FromentLorenzo/2024InternshipWatermeterAICam/test pictures/5.jpg

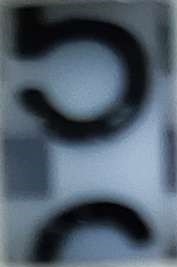
test pictures/5.jpg
