FromentLorenzo/2024InternshipWatermeterAICam/test pictures/8.jpg

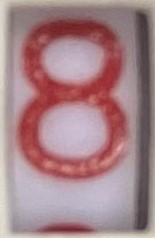
test pictures/8.jpg
