FromentLorenzo/2024InternshipWatermeterAICam/test pictures/23.jpg

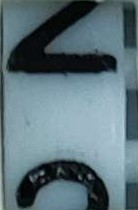
test pictures/23.jpg
