FromentLorenzo/2024InternshipWatermeterAICam/test pictures/45.jpg

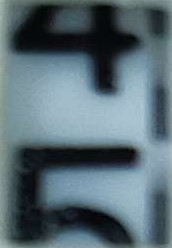
test pictures/45.jpg
