FromentLorenzo/2024InternshipWatermeterAICam/test pictures/56.jpg

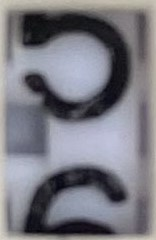
test pictures/56.jpg
