FromentLorenzo/2024InternshipWatermeterAICam/test pictures/78.jpg

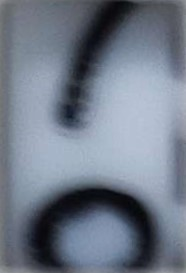
test pictures/78.jpg
