FromentLorenzo/2024InternshipWatermeterAICam/test pictures/IMG_8709.jpg

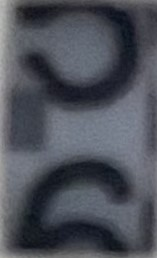
test pictures/IMG_8709.jpg
