FromentLorenzo/2024InternshipWatermeterAICam/test pictures/IMG_8921.jpg

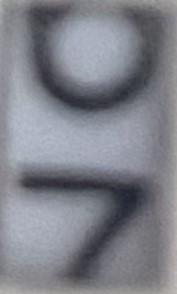
test pictures/IMG_8921.jpg
