FromentLorenzo/2024InternshipWatermeterAICam/test pictures/IMG_8922.jpg

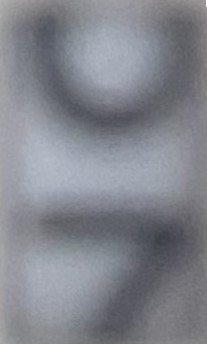
test pictures/IMG_8922.jpg
