FromentLorenzo/2024InternshipWatermeterAICam/test pictures/IMG_8923.jpg

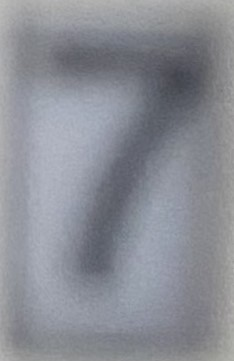
test pictures/IMG_8923.jpg
